Irdroid/USB-Infrared-Transmitter-v3/src/hwprofile.h

#ifndef HARDWARE_PROFILE_H
#define HARDWARE_PROFILE_H

#define HARDWARE_VERSION '3'
#define FIRMWARE_VERSION_H '5'
#define FIRMWARE_VERSION_L '3'

#define SAMPLE_ARRAY_SIZE 0x0040

struct _irtoy {
    unsigned char s[SAMPLE_ARRAY_SIZE];
};
#endif
